ClockWorkKid/ARM-Based-Piano/Figures/Pic/Piano.jpg

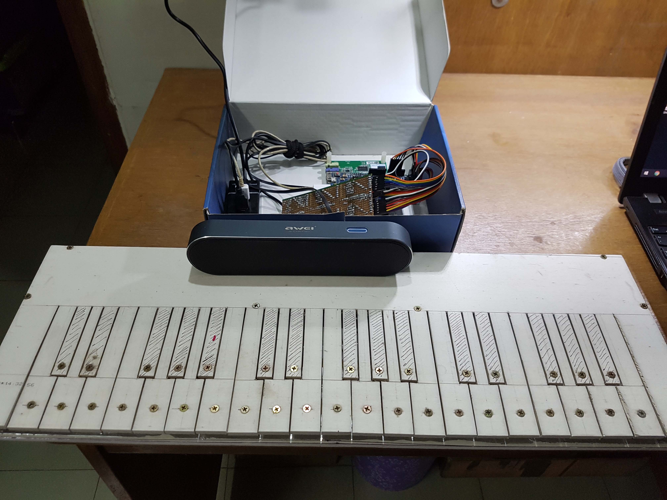
Figures/Pic/Piano.jpg
