ClockWorkKid/ARM-Based-Piano/Matlab Simulation/resample.jpg

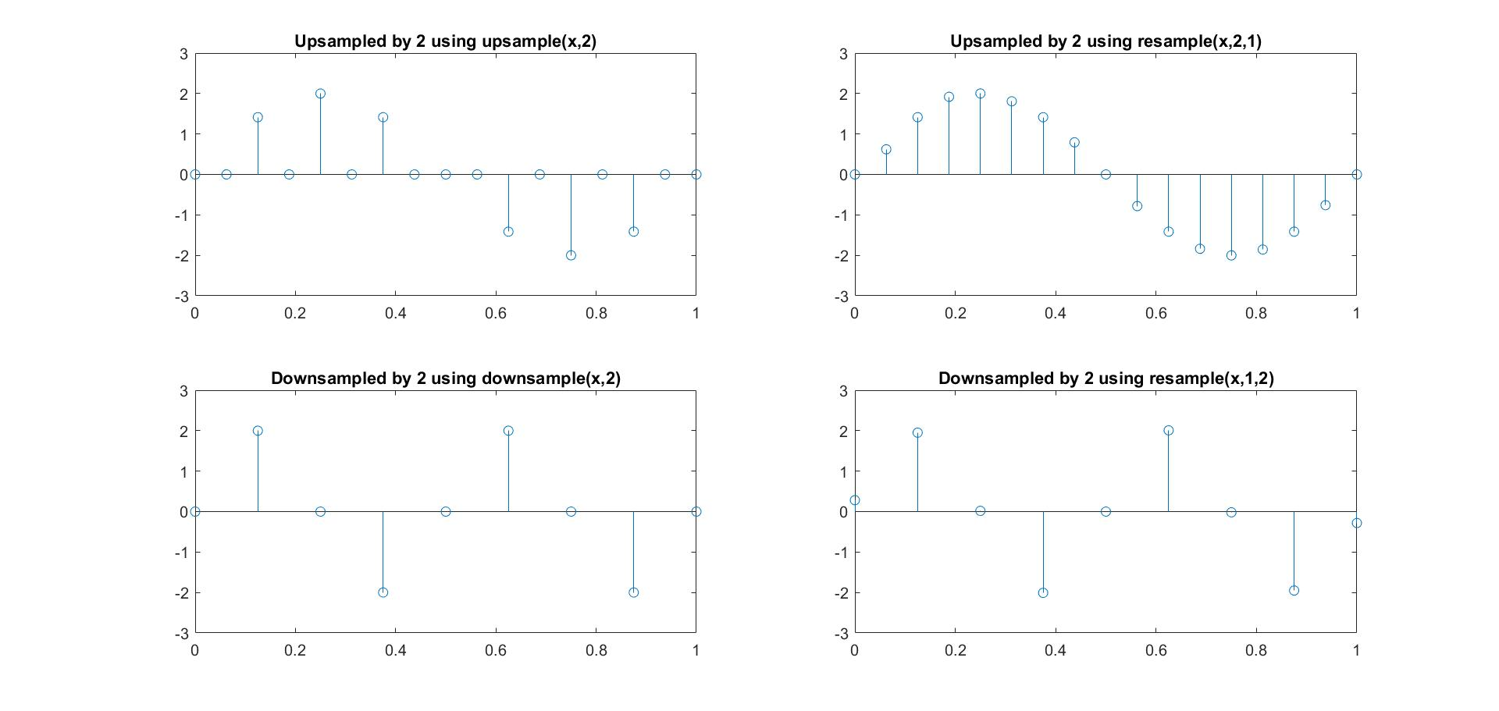
Matlab Simulation/resample.jpg
