ClockWorkKid/ARM-Based-Piano/Proteus Simulation/output.png

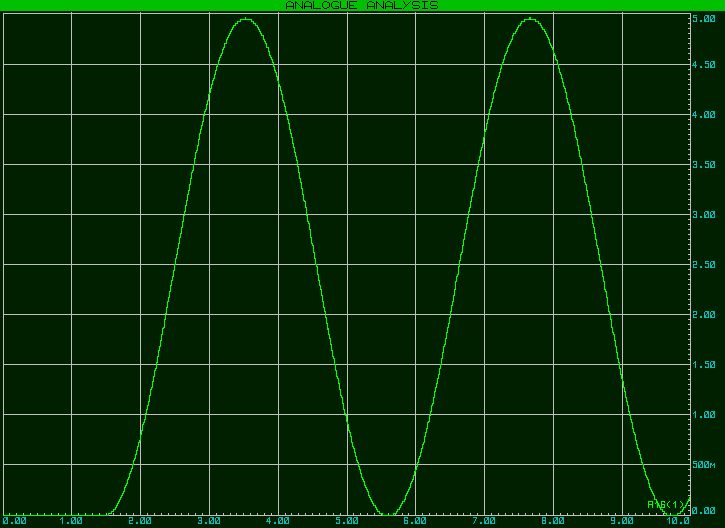
Proteus Simulation/output.png
