ClockWorkKid/ARM-Based-Piano/Working Matlab Simulation/Upsample Images/Downslice_1.png

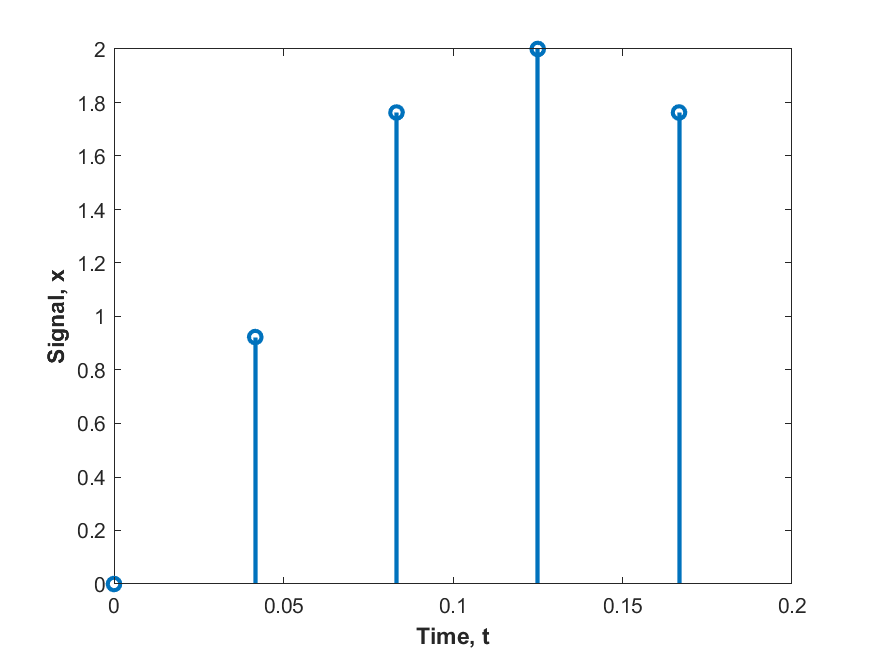
Working Matlab Simulation/Upsample Images/Downslice_1.png
