ClockWorkKid/ARM-Based-Piano/Working Matlab Simulation/Upsample Images/Downslice_2.png

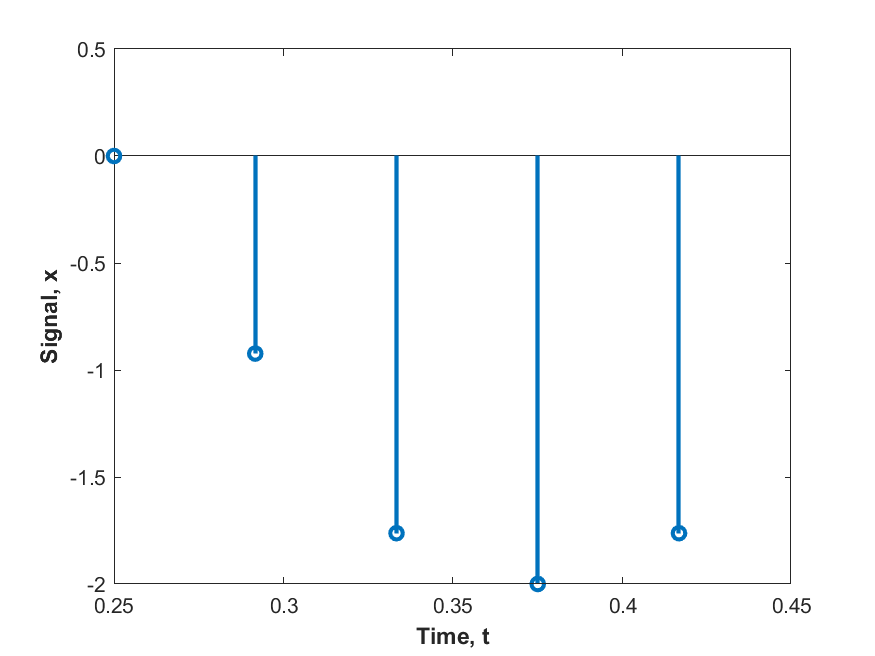
Working Matlab Simulation/Upsample Images/Downslice_2.png
