ClockWorkKid/ARM-Based-Piano/Working Matlab Simulation/Upsample Images/Slice_1.png

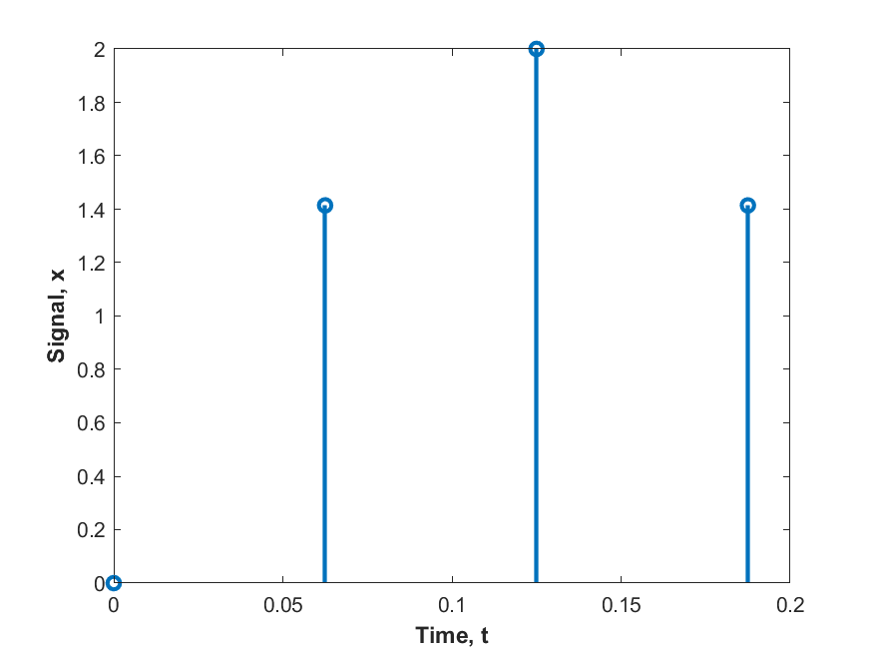
Working Matlab Simulation/Upsample Images/Slice_1.png
