ClockWorkKid/ARM-Based-Piano/Working Matlab Simulation/Upsample Images/Slice_2.png

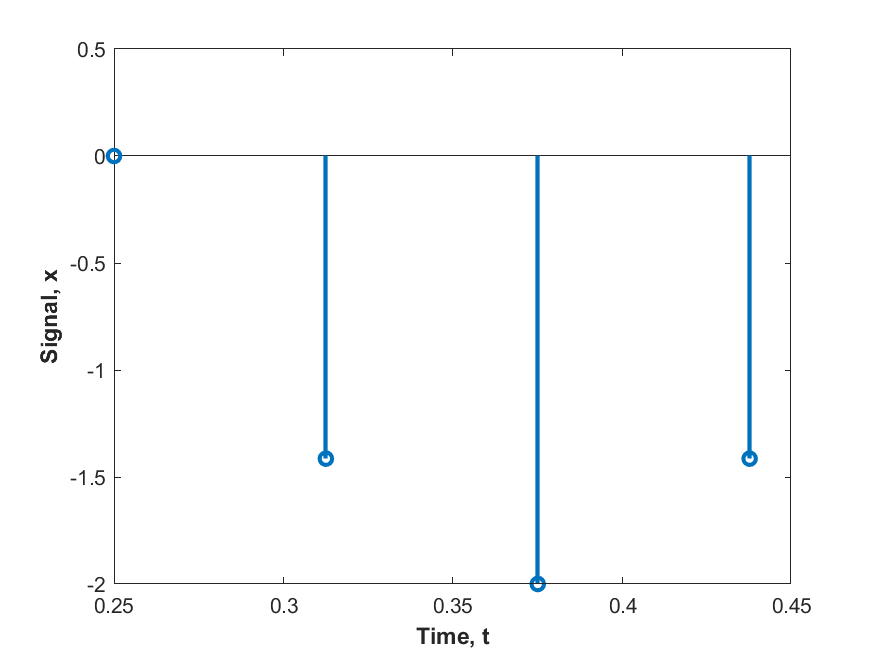
Working Matlab Simulation/Upsample Images/Slice_2.png
