ClockWorkKid/ARM-Based-Piano/Working Matlab Simulation/Upsample Images/Upsample02.png

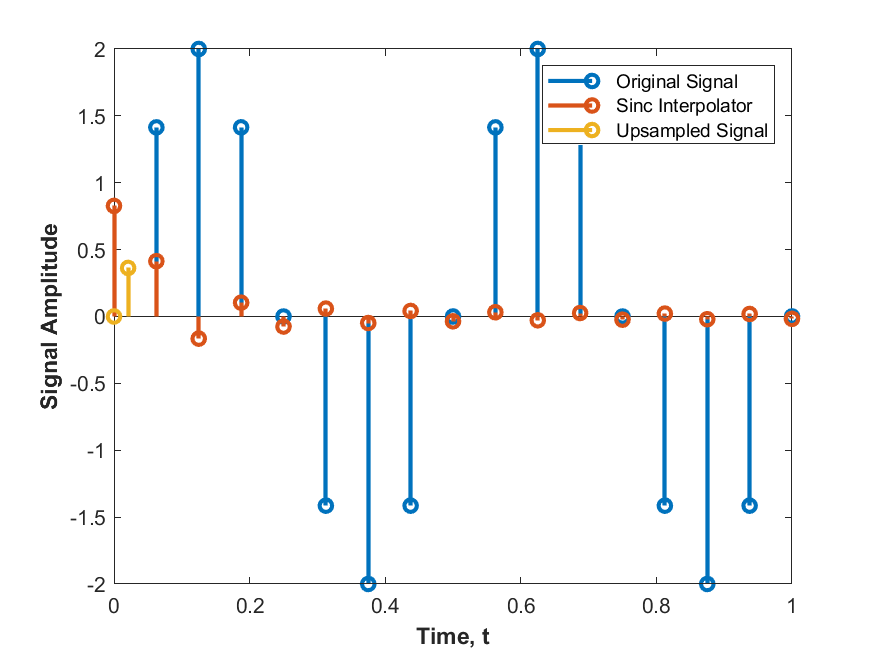
Working Matlab Simulation/Upsample Images/Upsample02.png
