ClockWorkKid/ARM-Based-Piano/Working Matlab Simulation/Upsample Images/Upsample04.png

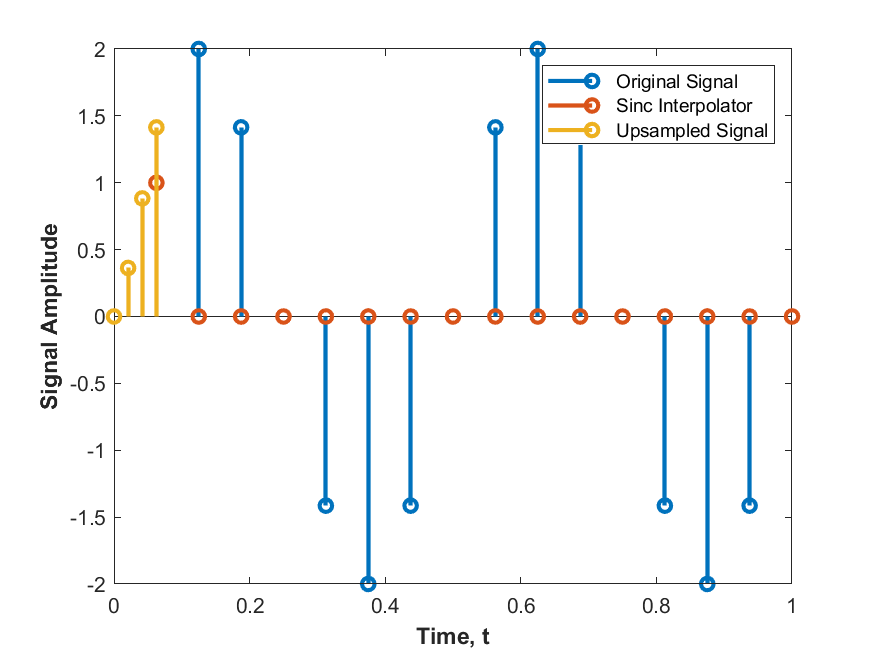
Working Matlab Simulation/Upsample Images/Upsample04.png
