ClockWorkKid/ARM-Based-Piano/Working Matlab Simulation/Upsample Images/Upsample07.png

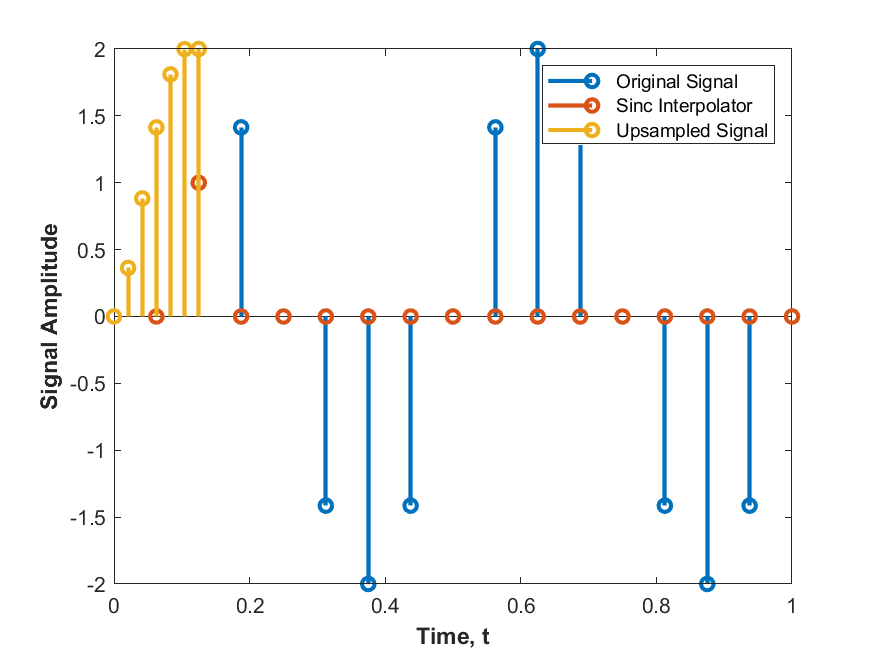
Working Matlab Simulation/Upsample Images/Upsample07.png
