ClockWorkKid/ARM-Based-Piano/Working Matlab Simulation/Upsample Images/Upsample11.png

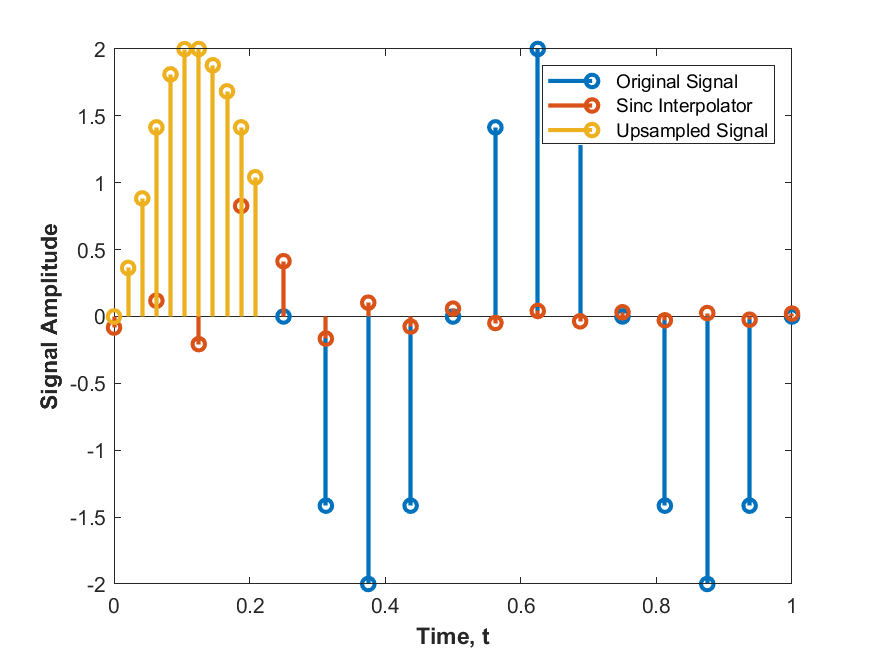
Working Matlab Simulation/Upsample Images/Upsample11.png
