ClockWorkKid/ARM-Based-Piano/Working Matlab Simulation/Upsample Images/Upsample17.png

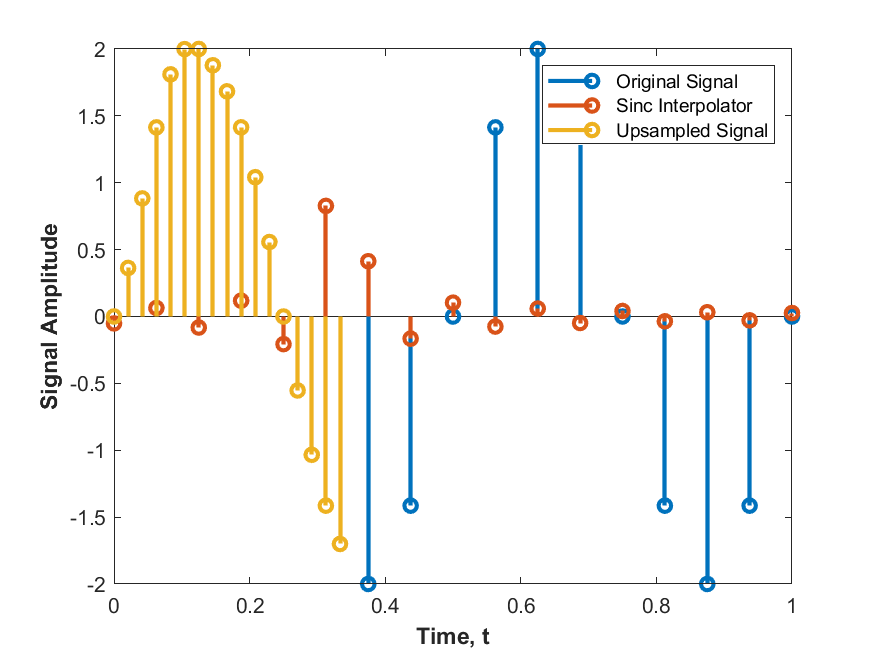
Working Matlab Simulation/Upsample Images/Upsample17.png
