ClockWorkKid/ARM-Based-Piano/Working Matlab Simulation/Upsample Images/Upslice_1.png

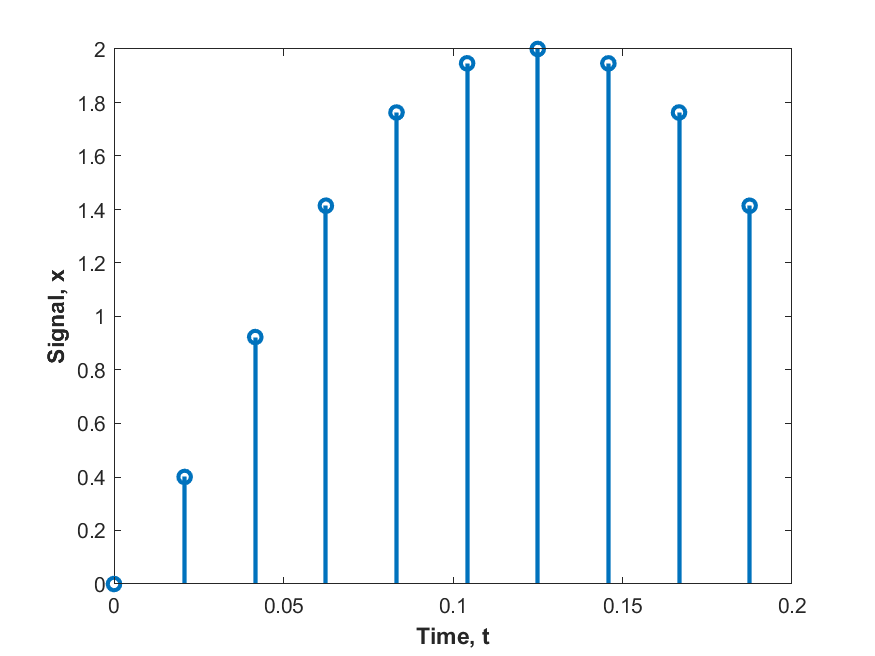
Working Matlab Simulation/Upsample Images/Upslice_1.png
