ClockWorkKid/ARM-Based-Piano/Working Matlab Simulation/Upsample Images/Upslice_2.png

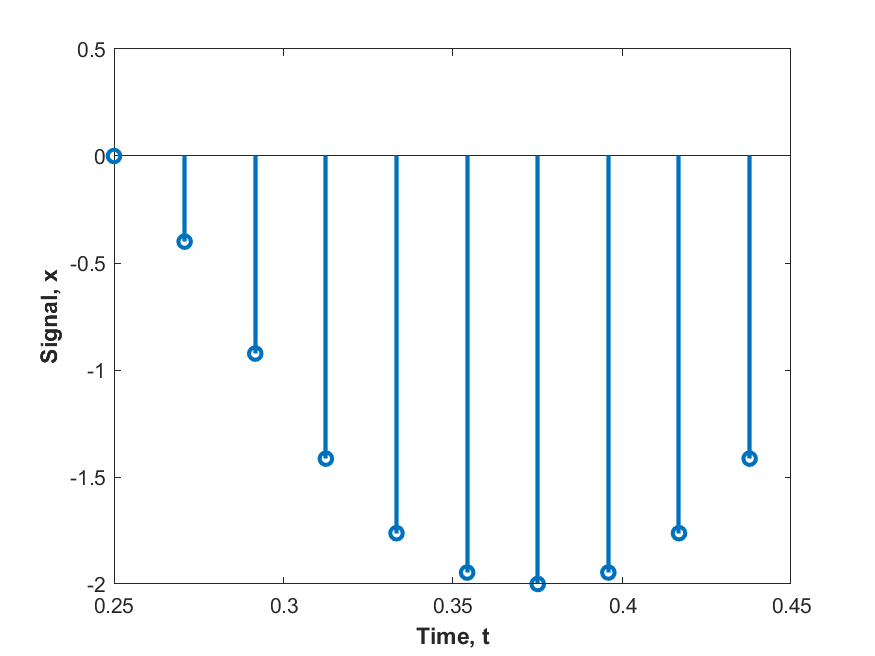
Working Matlab Simulation/Upsample Images/Upslice_2.png
