ClockWorkKid/ARM-Based-Piano/Solidworks Design/sharp_key.SLDPRT

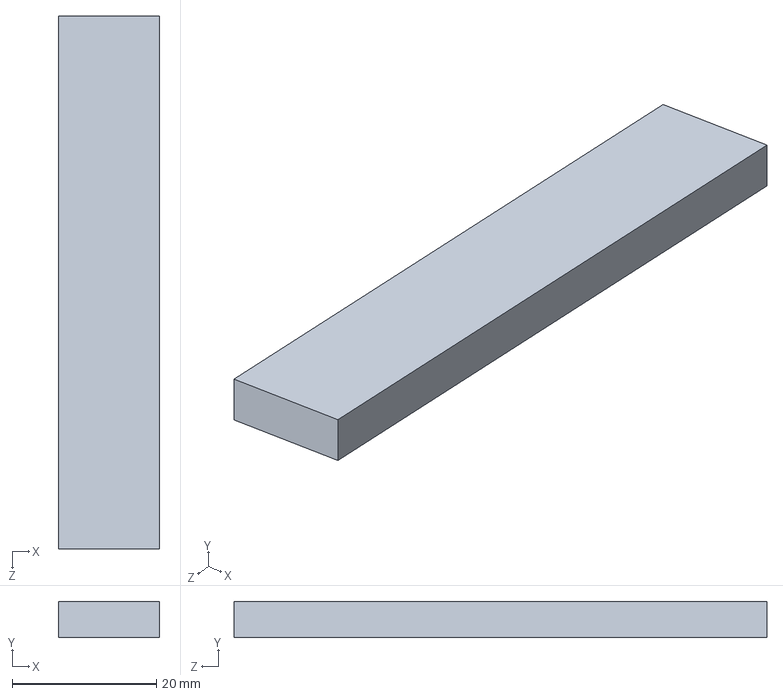
[picture p42: CAD file, 2021-07-27]
Solidworks Design/sharp_key.SLDPRT
14.0 x 5.00 x 74.0 mm
