ClockWorkKid/ARM-Based-Piano/Solidworks Design/Arduino Due/Switch - ESwitch - TLE3303.SLDPRT

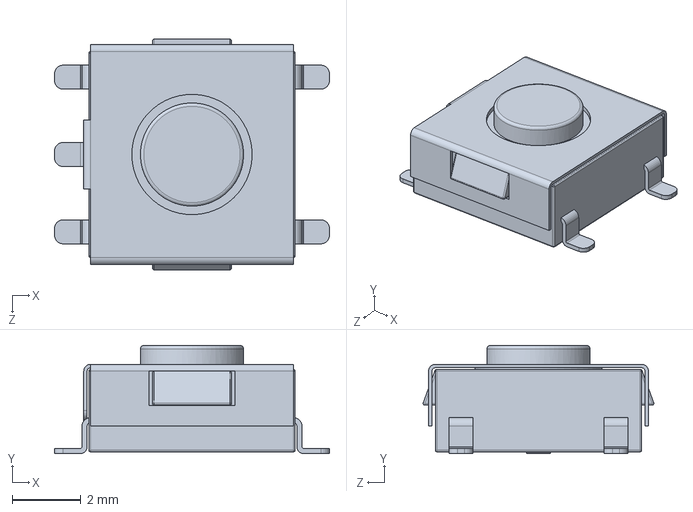
[picture p43: CAD file, 2021-07-27]
Solidworks Design/Arduino Due/Switch - ESwitch - TLE3303.SLDPRT
8.00 x 3.15 x 6.71 mm
