ClockWorkKid/ARM-Based-Piano/Solidworks Design/Arduino Due/Berg Header Receptacle long.SLDPRT

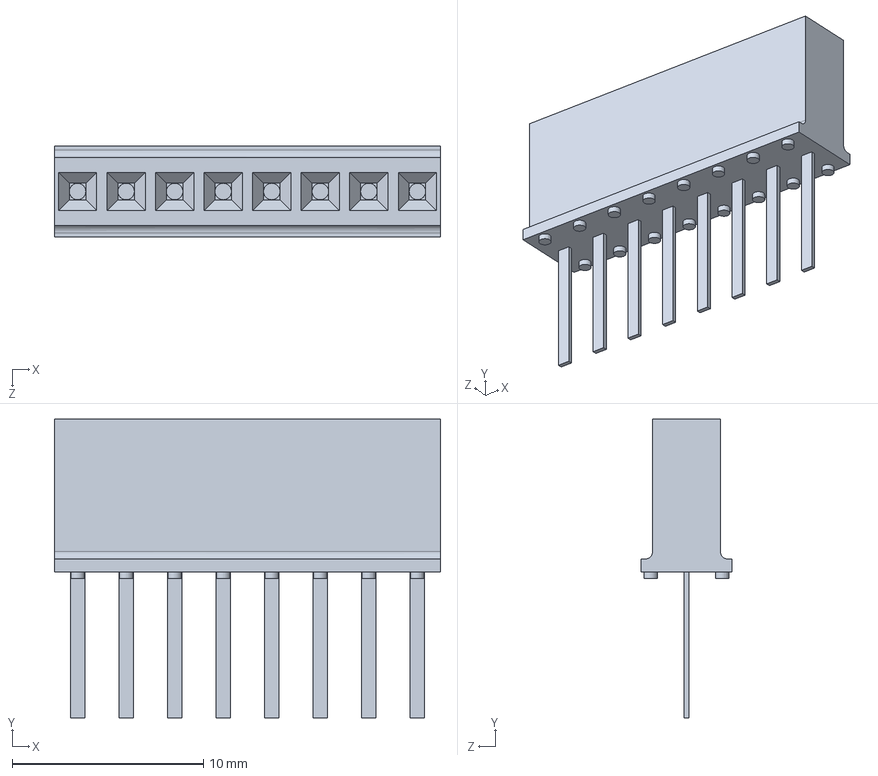
[picture p44: CAD file, 2021-07-27]
Solidworks Design/Arduino Due/Berg Header Receptacle long.SLDPRT
20.2 x 15.6 x 4.78 mm
