ClockWorkKid/ARM-Based-Piano/Solidworks Design/Arduino Due/Berg Header Receptacle 6.SLDPRT

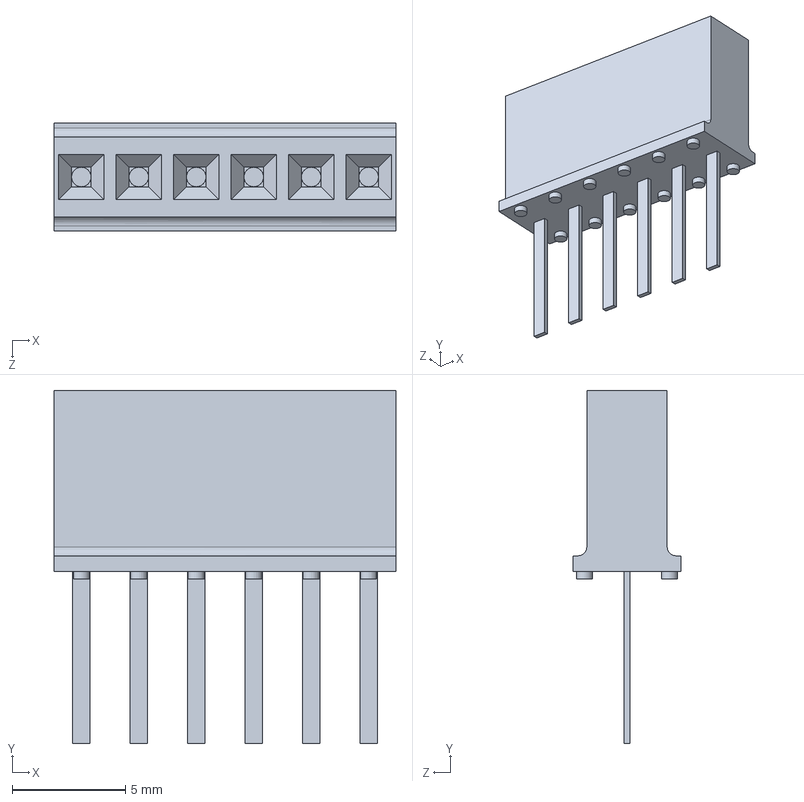
[picture p45: CAD file, 2021-07-27]
Solidworks Design/Arduino Due/Berg Header Receptacle 6.SLDPRT
15.1 x 15.6 x 4.78 mm
