ClockWorkKid/ARM-Based-Piano/Solidworks Design/Arduino Due/Microchip - Atmel - SAM3X8EAU.SLDPRT

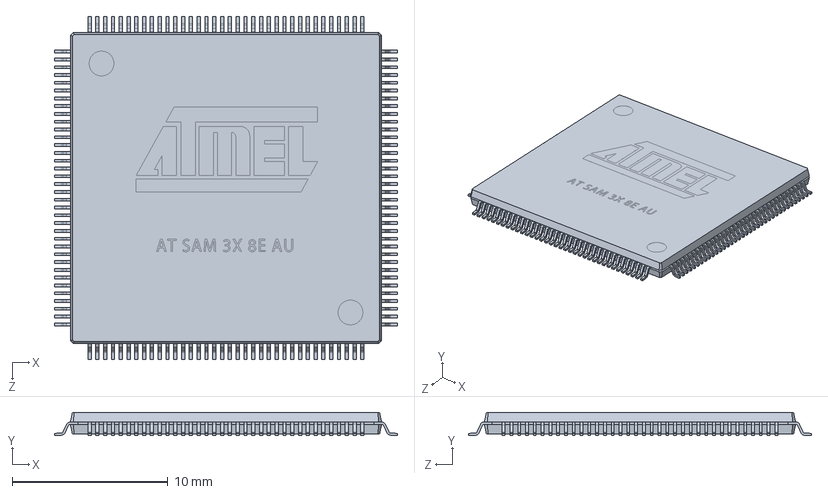
[picture p46: CAD file, 2021-07-27]
Solidworks Design/Arduino Due/Microchip - Atmel - SAM3X8EAU.SLDPRT
22.0 x 1.50 x 22.0 mm
