ClockWorkKid/ARM-Based-Piano/Solidworks Design/Arduino Due/Capacitor - Nichicon - UUR1C101MCL1GS.SLDPRT

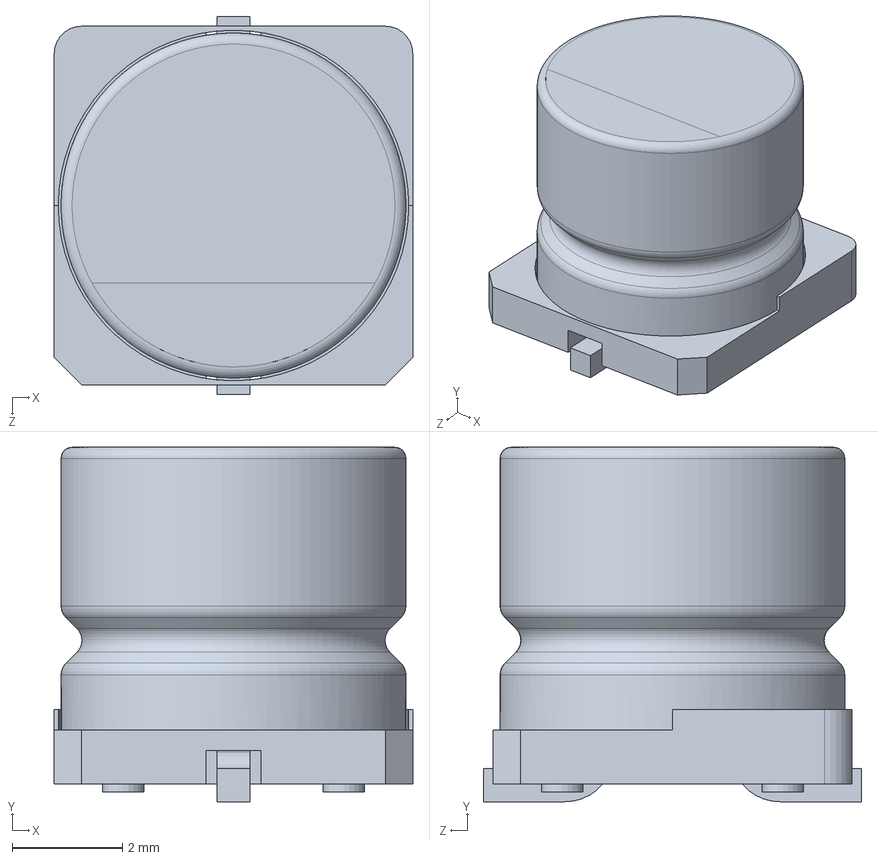
[picture p47: CAD file, 2021-07-27]
Solidworks Design/Arduino Due/Capacitor - Nichicon - UUR1C101MCL1GS.SLDPRT
6.50 x 6.42 x 6.85 mm
