ClockWorkKid/ARM-Based-Piano/Solidworks Design/Arduino Due/MicroUSB B - Hirose - ZX62D-B-5P8.SLDPRT

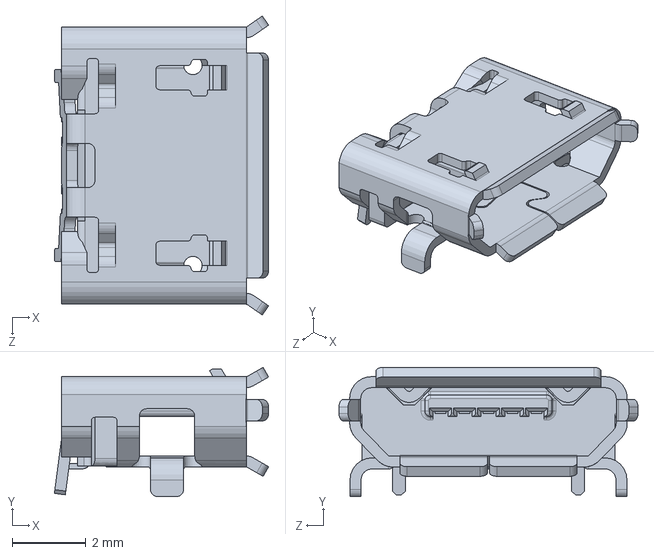
[picture p48: CAD file, 2021-07-27]
Solidworks Design/Arduino Due/MicroUSB B - Hirose - ZX62D-B-5P8.SLDPRT
5.80 x 3.50 x 8.09 mm
