ClockWorkKid/ARM-Based-Piano/Solidworks Design/Arduino Due/Berg Header Receptacle 2.54 x 10 - FCI - 66951-010LF.SLDPRT

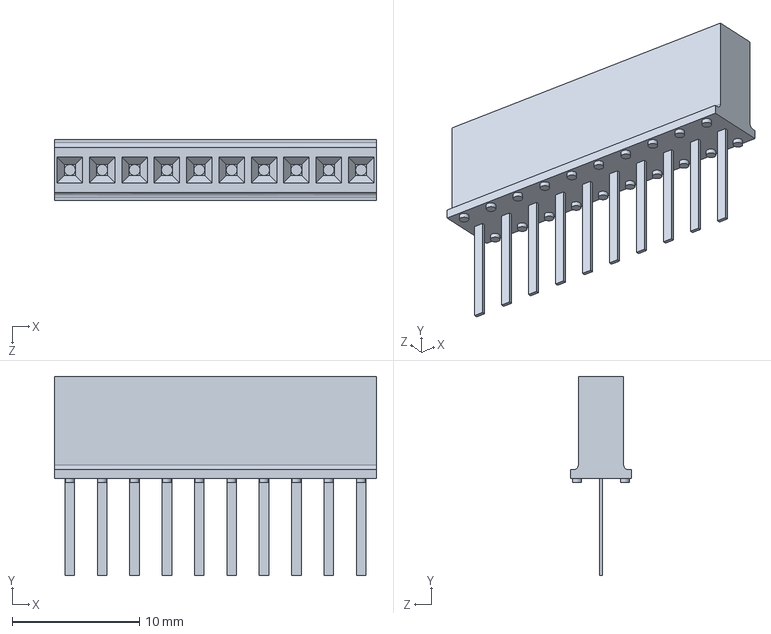
[picture p49: CAD file, 2021-07-27]
Solidworks Design/Arduino Due/Berg Header Receptacle 2.54 x 10 - FCI - 66951-010LF.SLDPRT
25.3 x 15.6 x 4.78 mm
