ClockWorkKid/ARM-Based-Piano/Solidworks Design/Arduino Due/Berg Header Receptacle 2.54 x 8 - FCI - 66951-008LF.SLDPRT

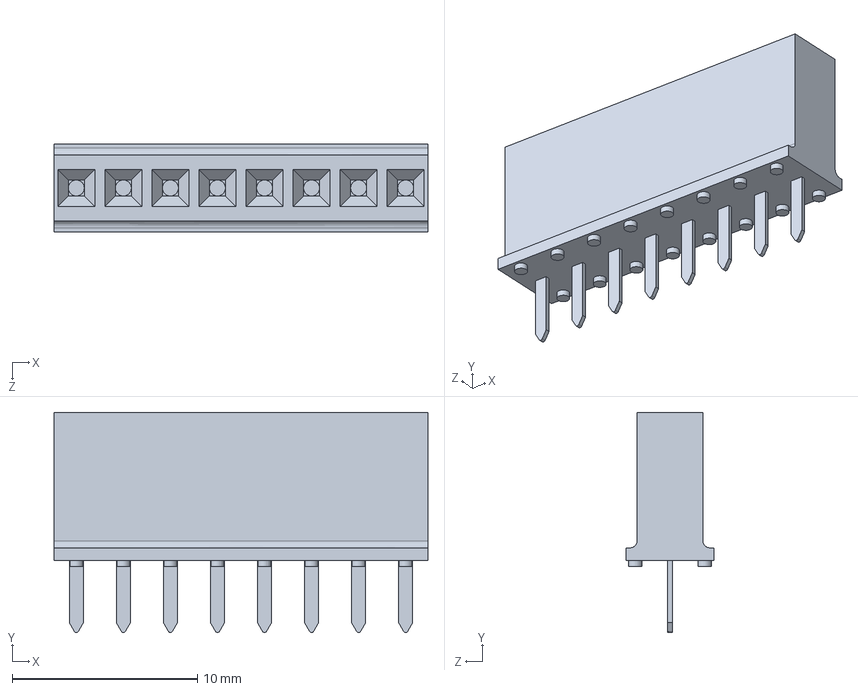
[picture p50: CAD file, 2021-07-27]
Solidworks Design/Arduino Due/Berg Header Receptacle 2.54 x 8 - FCI - 66951-008LF.SLDPRT
20.2 x 11.9 x 4.78 mm
