ClockWorkKid/ARM-Based-Piano/Solidworks Design/Arduino Due/MicroUSB AB - Hirose - ZX62-AB-5PA.SLDPRT

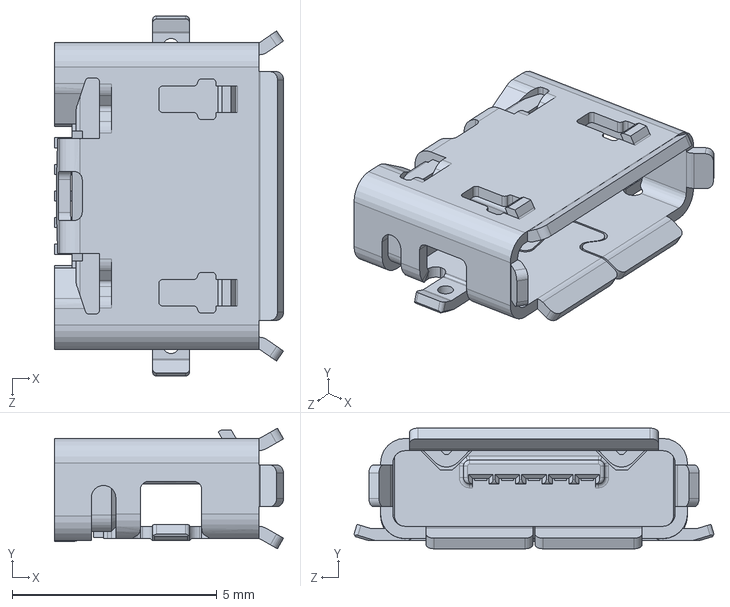
[picture p51: CAD file, 2021-07-27]
Solidworks Design/Arduino Due/MicroUSB AB - Hirose - ZX62-AB-5PA.SLDPRT
5.60 x 2.95 x 8.80 mm
